IurretaLHII-proj/kolobot-mechanics/CAD/PINZA/pinza(bego)/6-dof-robotic-arm-kit-with-servo-motors-10231211.jpg

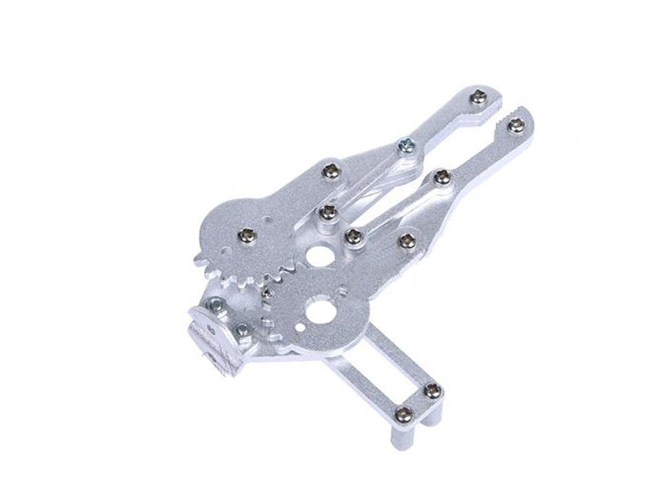
CAD/PINZA/pinza(bego)/6-dof-robotic-arm-kit-with-servo-motors-10231211.jpg
