IurretaLHII-proj/kolobot-mechanics/CAD/PINZA/pinza(bego)/AUREA.jpg

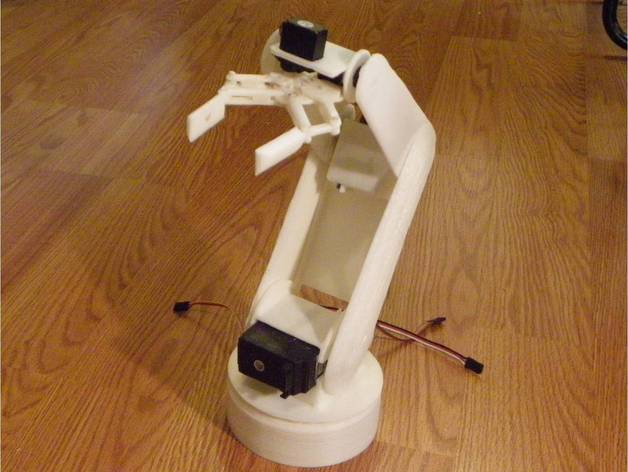
CAD/PINZA/pinza(bego)/AUREA.jpg
