IurretaLHII-proj/kolobot-mechanics/CAD/PINZA/pinza(bego)/descarga1.jpg

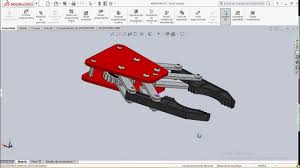
CAD/PINZA/pinza(bego)/descarga1.jpg
