IurretaLHII-proj/kolobot-mechanics/CAD/PINZA/pinza(bego)/descarga.jpg

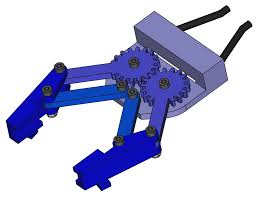
CAD/PINZA/pinza(bego)/descarga.jpg
