IurretaLHII-proj/kolobot-mechanics/CAD/PINZA/pinza(bego)/gripper2-solidworks.jpg

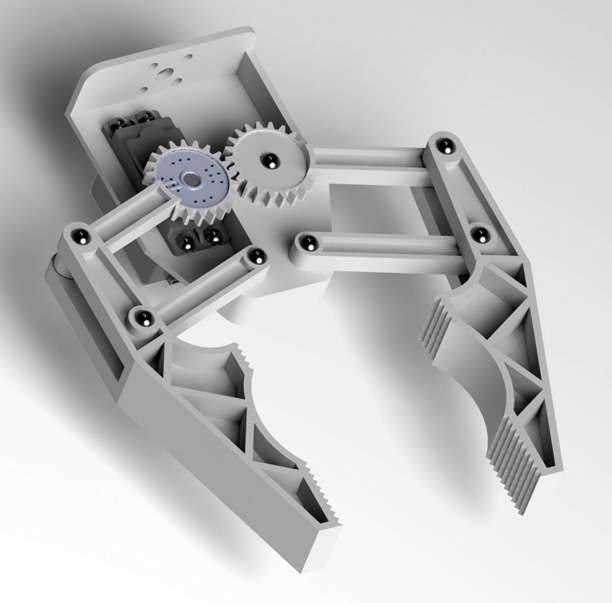
CAD/PINZA/pinza(bego)/gripper2-solidworks.jpg
