IurretaLHII-proj/kolobot-mechanics/CAD/PINZA/pinza(bego)/GRPA-KT-450x300.jpg

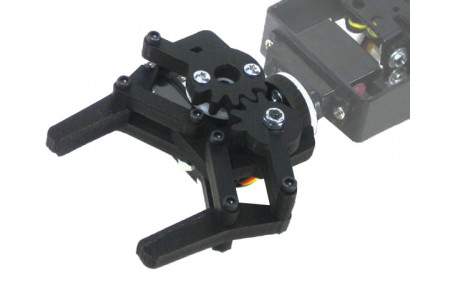
CAD/PINZA/pinza(bego)/GRPA-KT-450x300.jpg
