IurretaLHII-proj/kolobot-mechanics/CAD/PINZA/pinza(bego)/images1.jpg

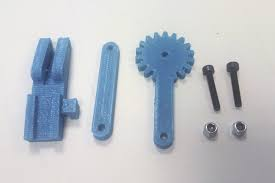
CAD/PINZA/pinza(bego)/images1.jpg
