IurretaLHII-proj/kolobot-mechanics/CAD/PINZA/pinza(bego)/images2.jpg

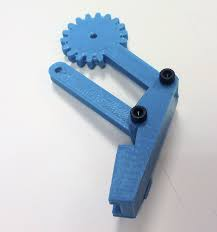
CAD/PINZA/pinza(bego)/images2.jpg
