IurretaLHII-proj/kolobot-mechanics/CAD/PINZA/pinza(bego)/images3.jpg

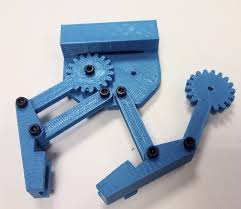
CAD/PINZA/pinza(bego)/images3.jpg
