IurretaLHII-proj/kolobot-mechanics/CAD/PINZA/pinza(bego)/AURREA/Arm_A3.stl

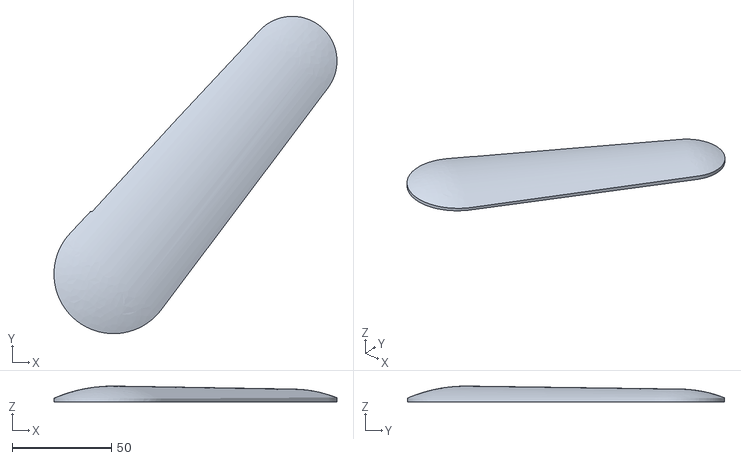
[picture p36: CAD file, 2022-01-14]
CAD/PINZA/pinza(bego)/AURREA/Arm_A3.stl
142.5 x 159.7 x 8.00
