IurretaLHII-proj/kolobot-mechanics/CAD/PINZA/pinza(bego)/robotic-arm-48.snapshot.6/MECCANO/PLASTIC GEAR.sldprt

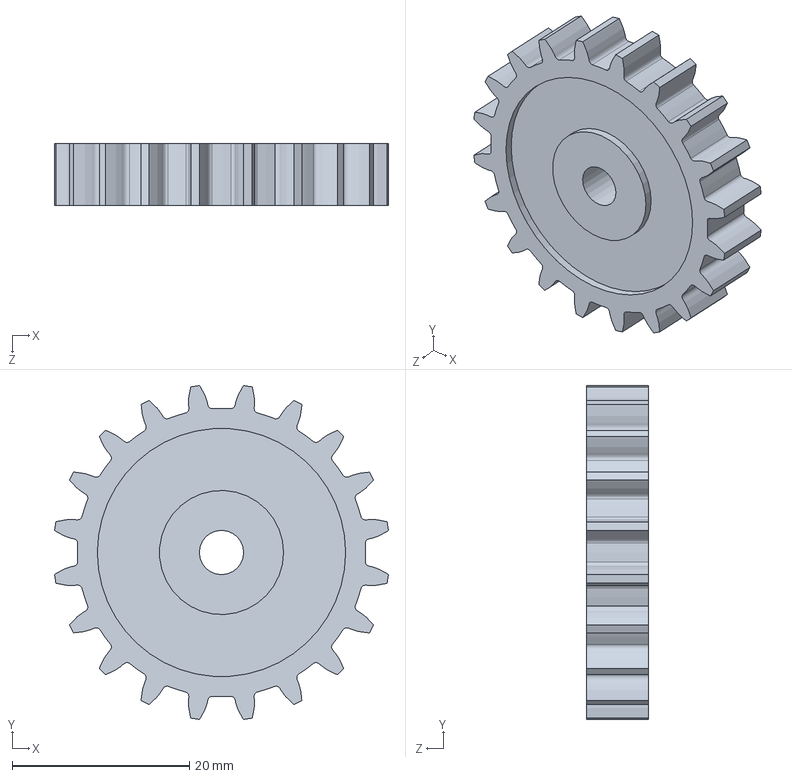
[picture p37: CAD file, 2022-01-14]
CAD/PINZA/pinza(bego)/robotic-arm-48.snapshot.6/MECCANO/PLASTIC GEAR.sldprt
37.7 x 37.7 x 7.00 mm
