IurretaLHII-proj/kolobot-mechanics/CAD/BIBRAZO/SOPORTE/tmp.stp

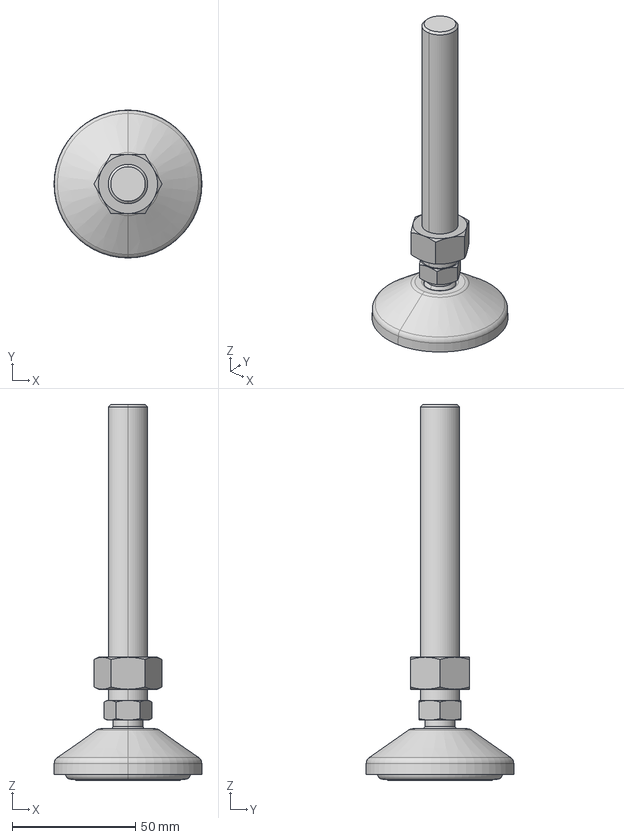
[picture p38: CAD file, 2022-01-14]
CAD/BIBRAZO/SOPORTE/tmp.stp
60.0 x 60.0 x 152.5 mm
