IurretaLHII-proj/kolobot-mechanics/CAD/PINZA/pinza(bego)/AURREA/Holder_omega_.stl

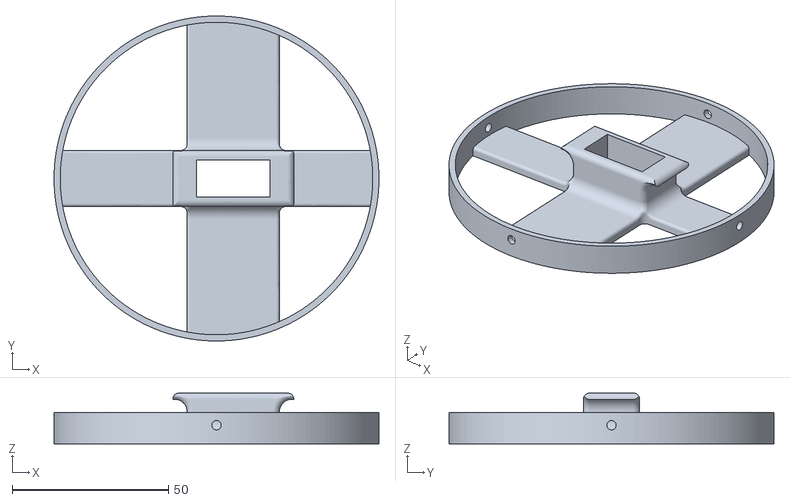
[picture p39: CAD file, 2022-01-14]
CAD/PINZA/pinza(bego)/AURREA/Holder_omega_.stl
104.0 x 104.0 x 16.3
