IurretaLHII-proj/kolobot-mechanics/CAD/PINZA/pinza(bego)/robotic-arm-48.snapshot.6/MECCANO/GRIP.sldprt

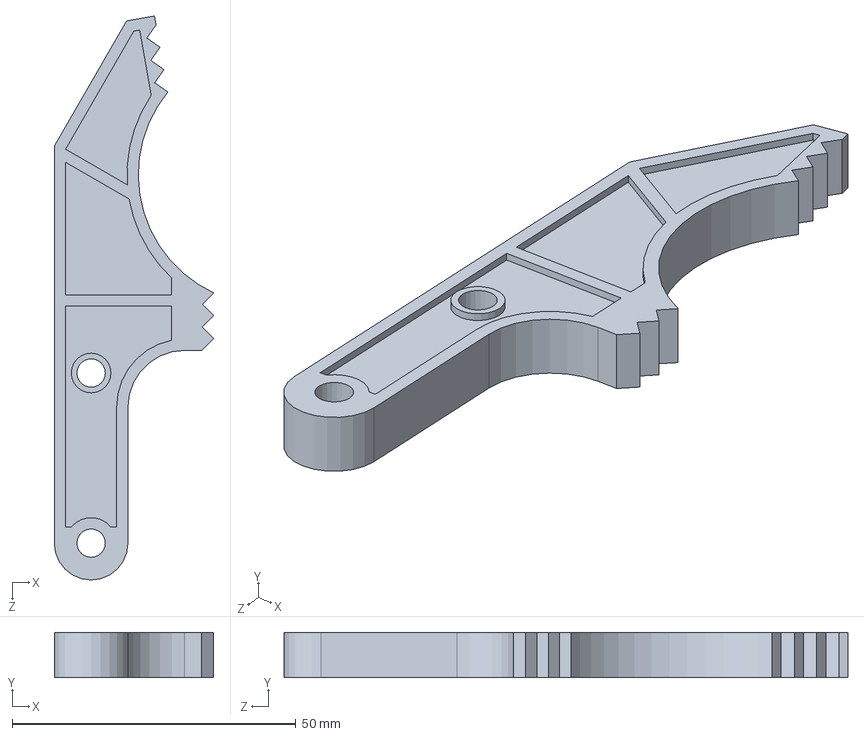
[picture p40: CAD file, 2022-01-14]
CAD/PINZA/pinza(bego)/robotic-arm-48.snapshot.6/MECCANO/GRIP.sldprt
28.1 x 8.00 x 99.5 mm
