IurretaLHII-proj/kolobot-mechanics/CAD/PINZA/STL artxiboak/CUBIERTA.stl

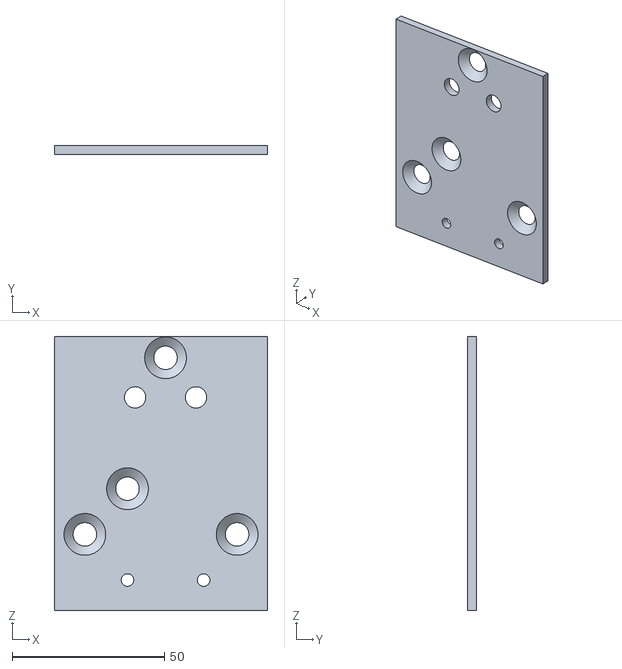
[picture p41: CAD file, 2022-01-14]
CAD/PINZA/STL artxiboak/CUBIERTA.stl
70.0 x 3.00 x 90.0
