IurretaLHII-proj/kolobot-mechanics/CAD/BIBRAZO/SOPORTE/21_0978_0_1.igs

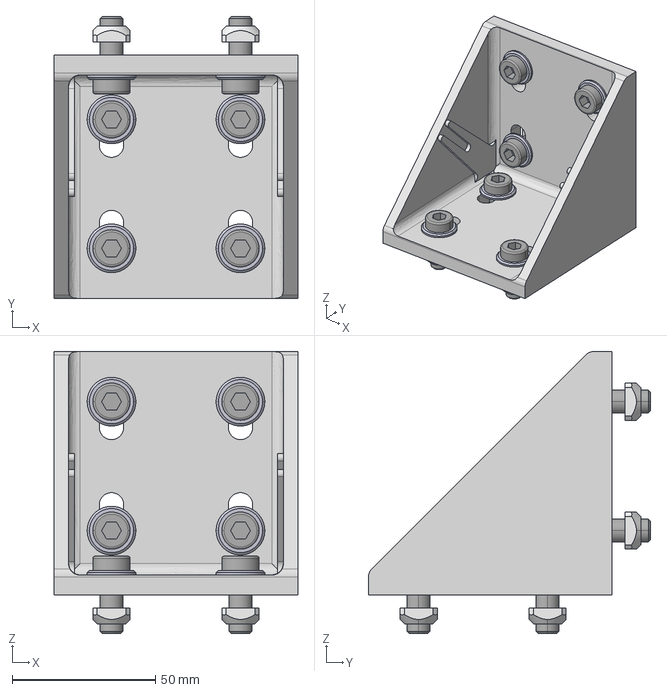
[picture p42: CAD file, 2022-01-14]
CAD/BIBRAZO/SOPORTE/21_0978_0_1.igs
85.0 x 98.4 x 98.4 mm
