IurretaLHII-proj/kolobot-mechanics/CAD/PINZA/pinza(bego)/AURREA/Arm_C3.stl

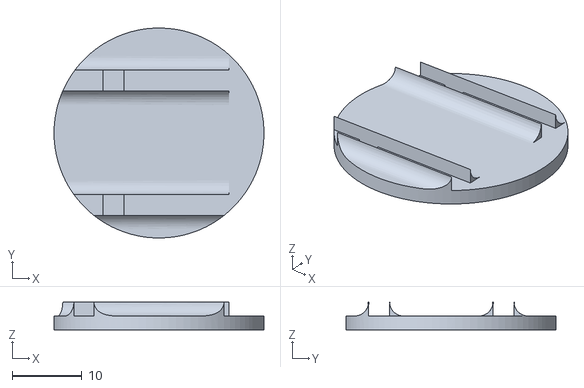
[picture p43: CAD file, 2022-01-14]
CAD/PINZA/pinza(bego)/AURREA/Arm_C3.stl
30.0 x 30.0 x 4.00
