IurretaLHII-proj/kolobot-mechanics/CAD/PINZA/pinza(bego)/robotic-arm-48.snapshot.6/MECCANO/BASE.SLDPRT

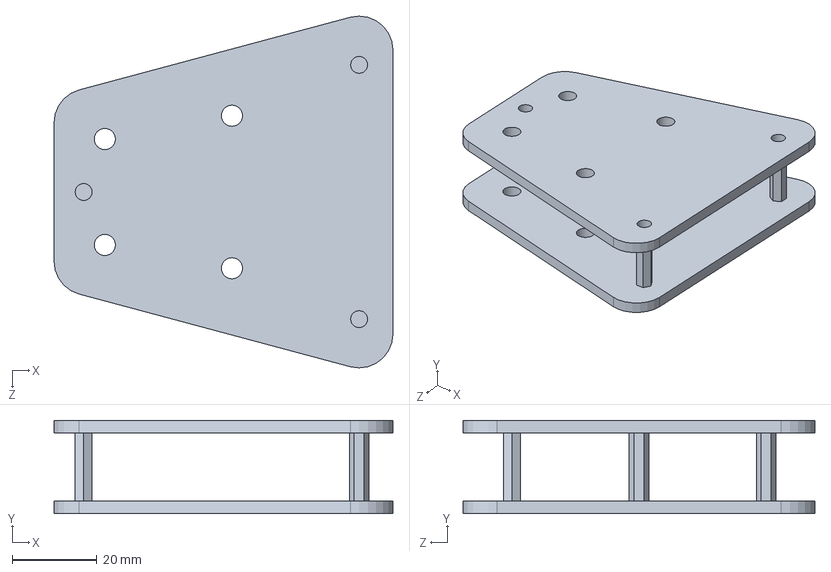
[picture p44: CAD file, 2022-01-14]
CAD/PINZA/pinza(bego)/robotic-arm-48.snapshot.6/MECCANO/BASE.SLDPRT
80.0 x 22.0 x 83.0 mm
