IurretaLHII-proj/kolobot-mechanics/CAD/PINZA/STL artxiboak/BRAZO PINZA (plastico-B).stl

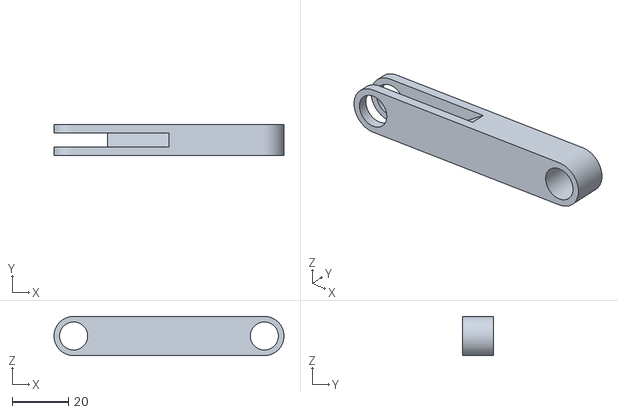
[picture p45: CAD file, 2022-01-14]
CAD/PINZA/STL artxiboak/BRAZO PINZA (plastico-B).stl
82.0 x 11.0 x 14.0
