IurretaLHII-proj/kolobot-mechanics/CAD/BIBRAZO/SOPORTE/21_1473_0_1.igs

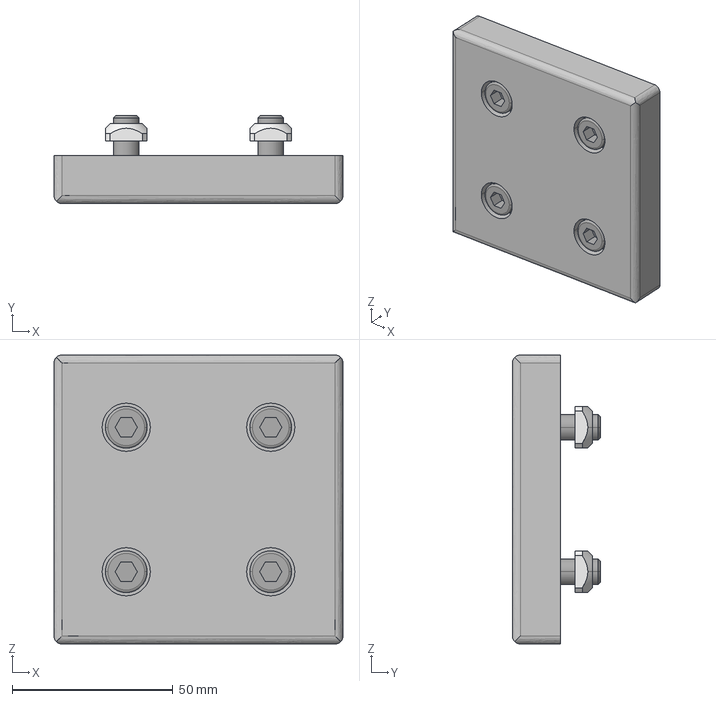
[picture p46: CAD file, 2022-01-14]
CAD/BIBRAZO/SOPORTE/21_1473_0_1.igs
90.0 x 27.5 x 90.0 mm
