IurretaLHII-proj/kolobot-mechanics/CAD/PINZA/pinza(bego)/AURREA/Arm_B3.stl

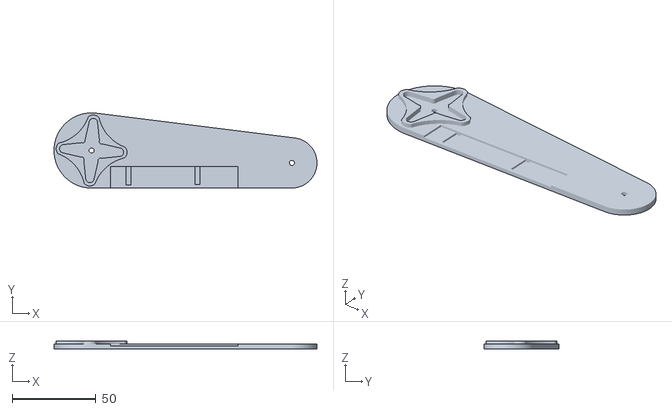
[picture p47: CAD file, 2022-01-14]
CAD/PINZA/pinza(bego)/AURREA/Arm_B3.stl
157.3 x 45.0 x 5.00
