IurretaLHII-proj/kolobot-mechanics/CAD/PINZA/pinza(bego)/robotic-arm-48.snapshot.6/MECCANO/ARM ROBOTIC.STEP

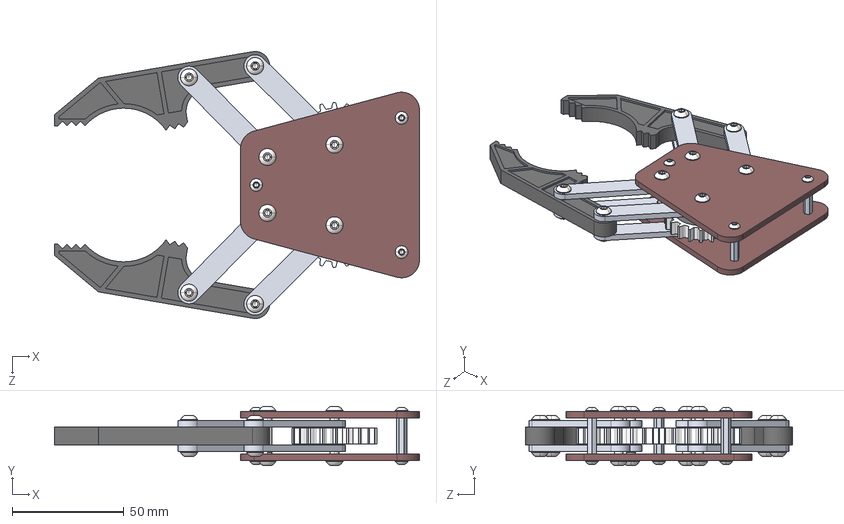
[picture p48: CAD file, 2022-01-14]
CAD/PINZA/pinza(bego)/robotic-arm-48.snapshot.6/MECCANO/ARM ROBOTIC.STEP
163.2 x 26.4 x 119.4 mm
socket button head cap screw_am_B18.3.4M - 4 x 0.7 x 4 SBHCS --N x 8
socket button head cap screw_am_B18.3.4M - 3 x 0.5 x 3 SBHCS --N x 6
BASE
socket button head cap screw_am_B18.3.4M - 4 x 0.7 x 8 SBHCS --N x 4
socket button head cap screw_am_B18.3.4M - 4 x 0.7 x 20 SBHCS --N x 4
PCS1 x 8
PLASTIC GEAR x 2
GRIP x 2
