IurretaLHII-proj/kolobot-mechanics/CAD/PINZA/STL artxiboak/ANTEBRAZO7.stl

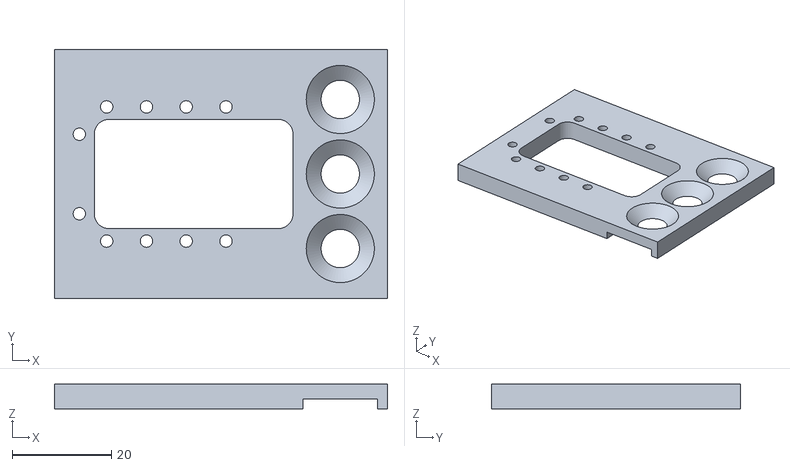
[picture p49: CAD file, 2022-01-14]
CAD/PINZA/STL artxiboak/ANTEBRAZO7.stl
67.0 x 50.0 x 5.00
