IurretaLHII-proj/kolobot-mechanics/CAD/PINZA/pinza(bego)/AURREA/Phalange_proximal_L.stl

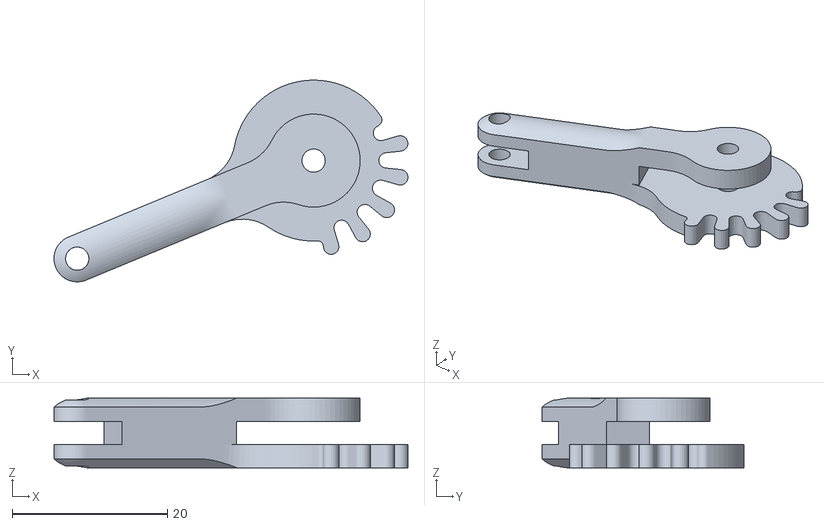
[picture p51: CAD file, 2022-01-14]
CAD/PINZA/pinza(bego)/AURREA/Phalange_proximal_L.stl
45.6 x 26.0 x 9.00
