IurretaLHII-proj/kolobot-mechanics/CAD/PINZA/STL artxiboak/BRAZO DE PLASTICO(sin cortar).stl

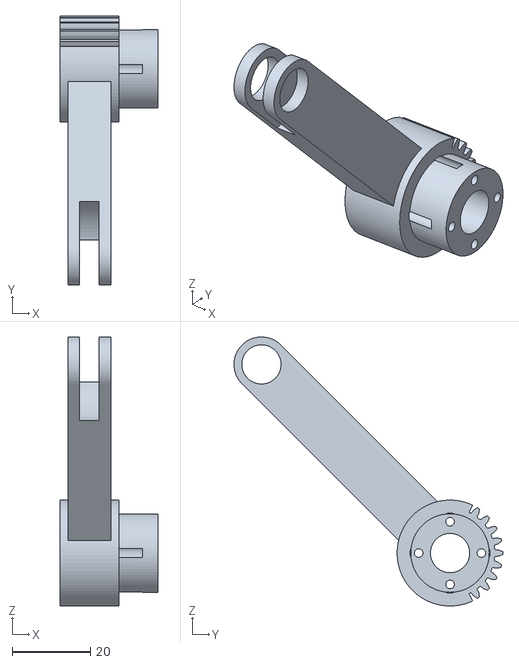
[picture p52: CAD file, 2022-01-14]
CAD/PINZA/STL artxiboak/BRAZO DE PLASTICO(sin cortar).stl
25.0 x 68.6 x 68.6
