IurretaLHII-proj/kolobot-mechanics/CAD/BIBRAZO/SOPORTE/20_1019_0_1_3.igs

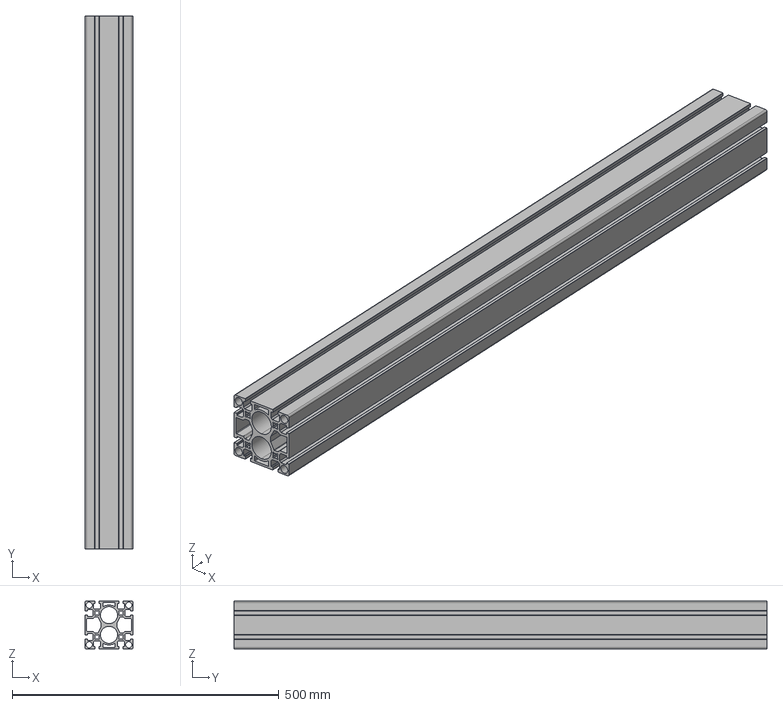
[picture p53: CAD file, 2022-01-14]
CAD/BIBRAZO/SOPORTE/20_1019_0_1_3.igs
90.0 x 1000.0 x 90.0 mm
