IurretaLHII-proj/kolobot-mechanics/CAD/PINZA/pinza(bego)/AURREA/Arm_A_.stl

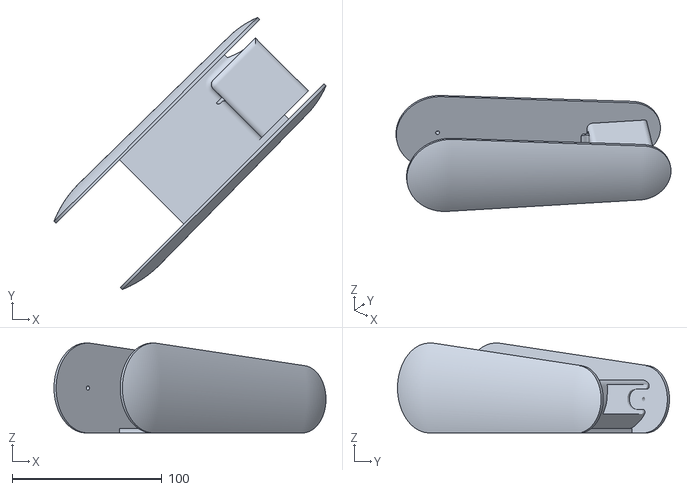
[picture p54: CAD file, 2022-01-14]
CAD/PINZA/pinza(bego)/AURREA/Arm_A_.stl
181.7 x 181.7 x 60.0
