IurretaLHII-proj/kolobot-mechanics/CAD/PINZA/STL artxiboak/BRAZO DE PLASTICO(cortado).stl

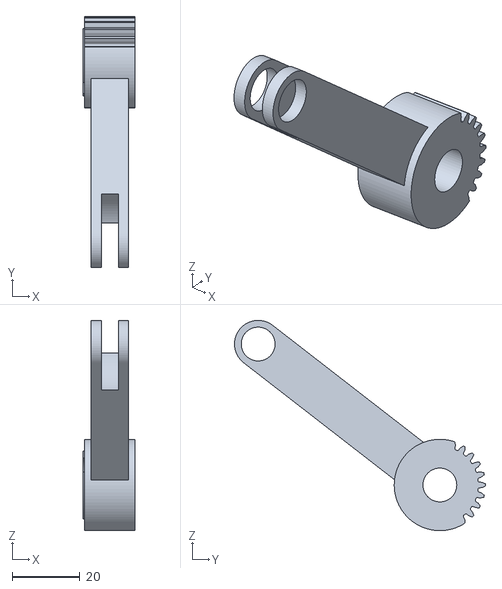
[picture p55: CAD file, 2022-01-14]
CAD/PINZA/STL artxiboak/BRAZO DE PLASTICO(cortado).stl
15.5 x 74.2 x 62.2
