IurretaLHII-proj/kolobot-mechanics/CAD/BIBRAZO/SOPORTE/22_1008_2_1.igs

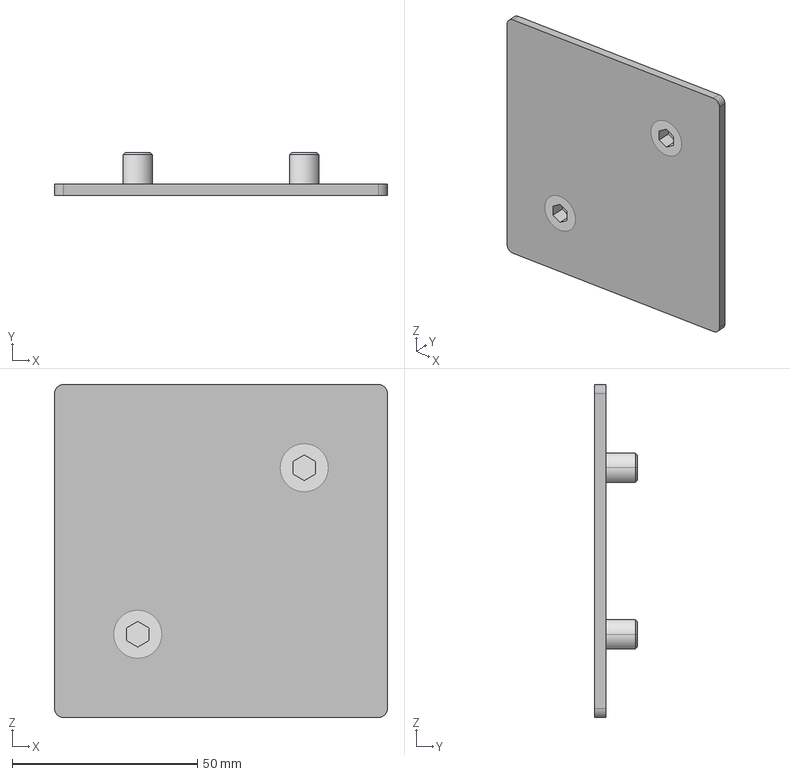
[picture p56: CAD file, 2022-01-14]
CAD/BIBRAZO/SOPORTE/22_1008_2_1.igs
90.0 x 11.5 x 90.0 mm
