IurretaLHII-proj/kolobot-mechanics/CAD/PINZA/pinza(bego)/AURREA/Arm_C2.stl

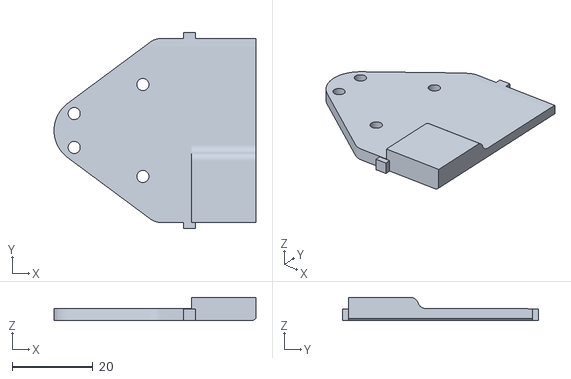
[picture p57: CAD file, 2022-01-14]
CAD/PINZA/pinza(bego)/AURREA/Arm_C2.stl
50.0 x 48.5 x 5.78
