IurretaLHII-proj/kolobot-mechanics/CAD/PINZA/STL artxiboak/GARRA plastico.stl

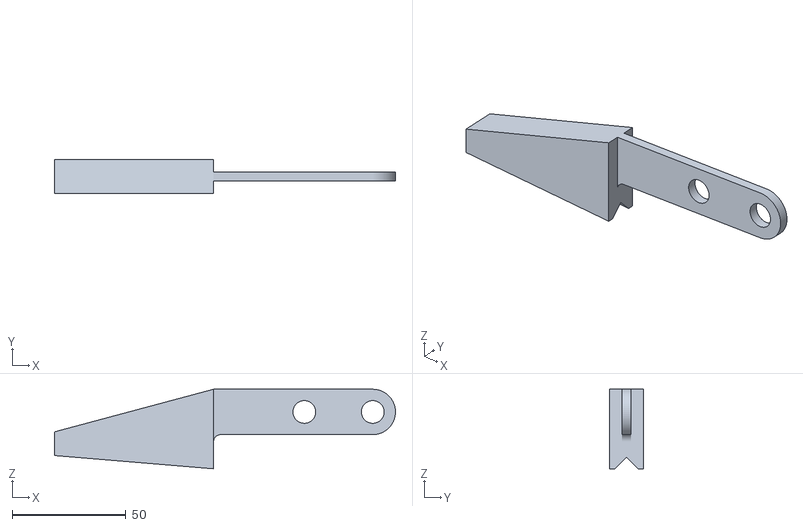
[picture p58: CAD file, 2022-01-14]
CAD/PINZA/STL artxiboak/GARRA plastico.stl
150.0 x 15.0 x 35.0
