IurretaLHII-proj/kolobot-mechanics/CAD/BIBRAZO/SOPORTE/20_1019_0_1_4.igs

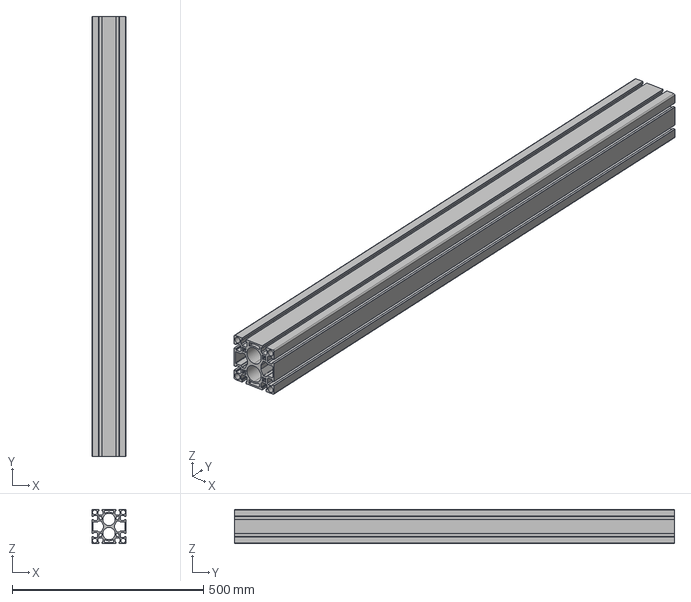
[picture p59: CAD file, 2022-01-14]
CAD/BIBRAZO/SOPORTE/20_1019_0_1_4.igs
90.0 x 1150.0 x 90.0 mm
