IurretaLHII-proj/kolobot-mechanics/CAD/PINZA/pinza(bego)/AURREA/Base_.stl

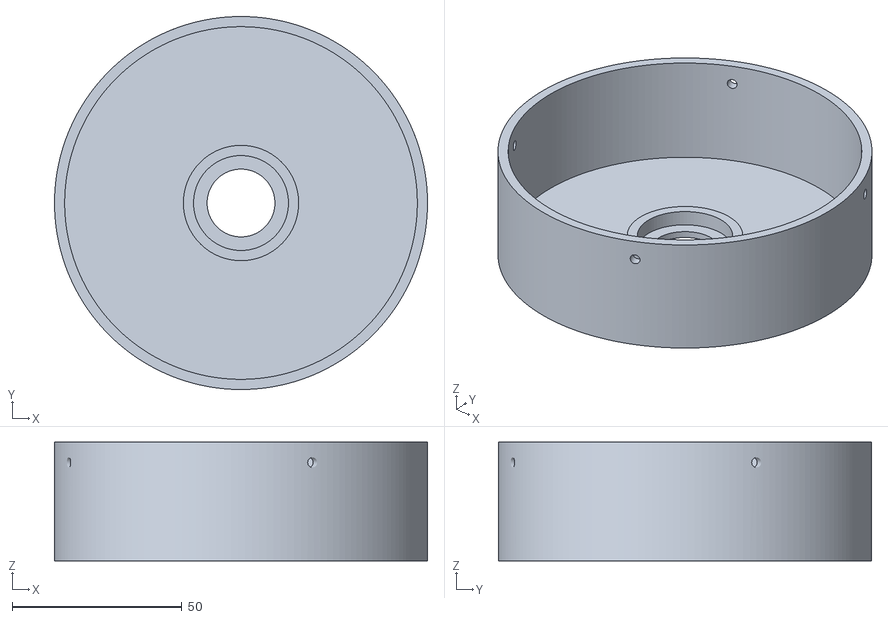
[picture p60: CAD file, 2022-01-14]
CAD/PINZA/pinza(bego)/AURREA/Base_.stl
110.0 x 110.0 x 35.0
