IurretaLHII-proj/kolobot-mechanics/CAD/PINZA/pinza(bego)/AURREA/Arm_B_.stl

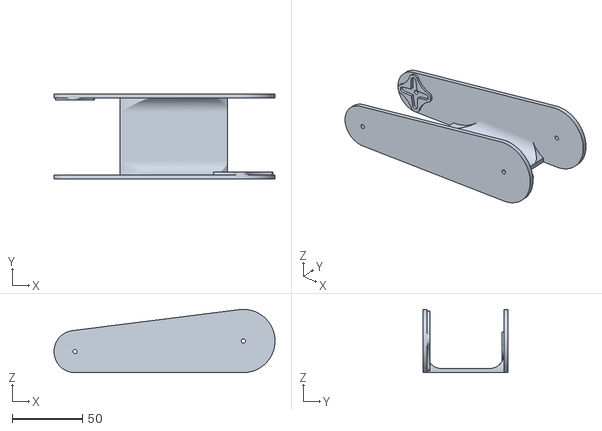
[picture p61: CAD file, 2022-01-14]
CAD/PINZA/pinza(bego)/AURREA/Arm_B_.stl
157.3 x 60.6 x 45.0
