IurretaLHII-proj/kolobot-mechanics/CAD/BIBRAZO/SOPORTE/20_1019_0_1_1.igs

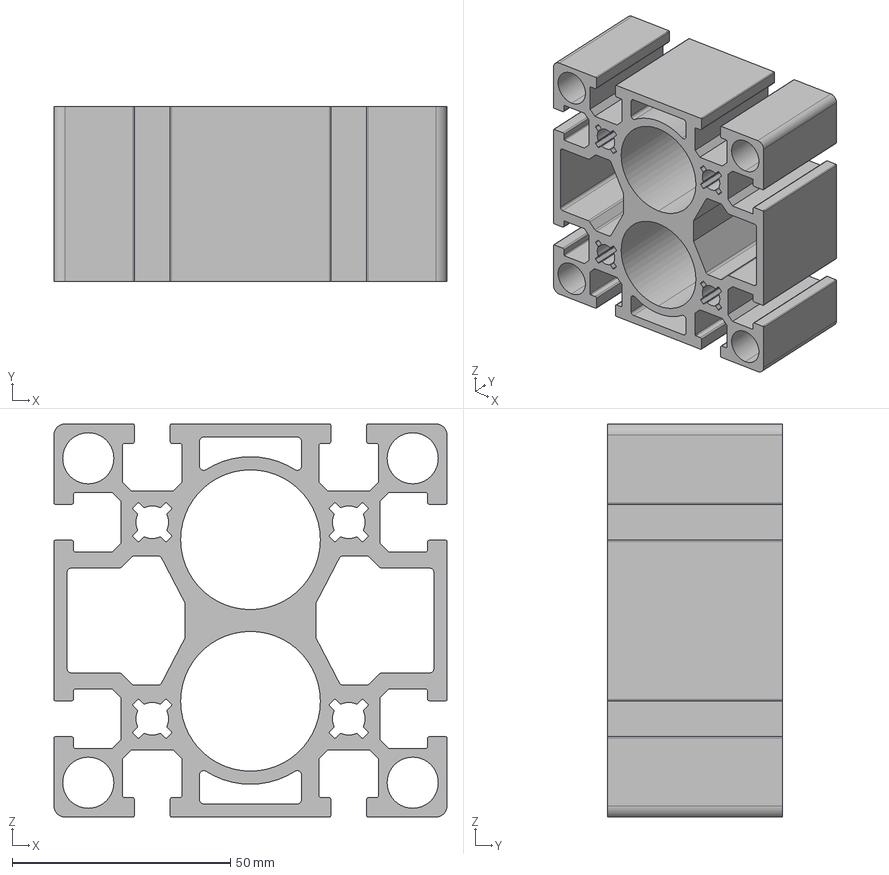
[picture p62: CAD file, 2022-01-14]
CAD/BIBRAZO/SOPORTE/20_1019_0_1_1.igs
90.0 x 40.0 x 90.0 mm
