IurretaLHII-proj/kolobot-mechanics/CAD/PINZA/pinza(bego)/AURREA/Arm_B2.stl

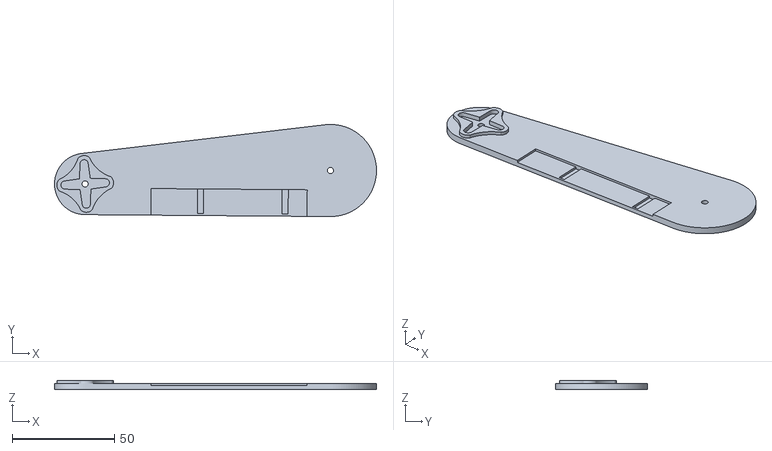
[picture p63: CAD file, 2022-01-14]
CAD/PINZA/pinza(bego)/AURREA/Arm_B2.stl
157.3 x 45.0 x 4.50
