IurretaLHII-proj/kolobot-mechanics/CAD/BIBRAZO/SOPORTE/20_1016_0_1.igs

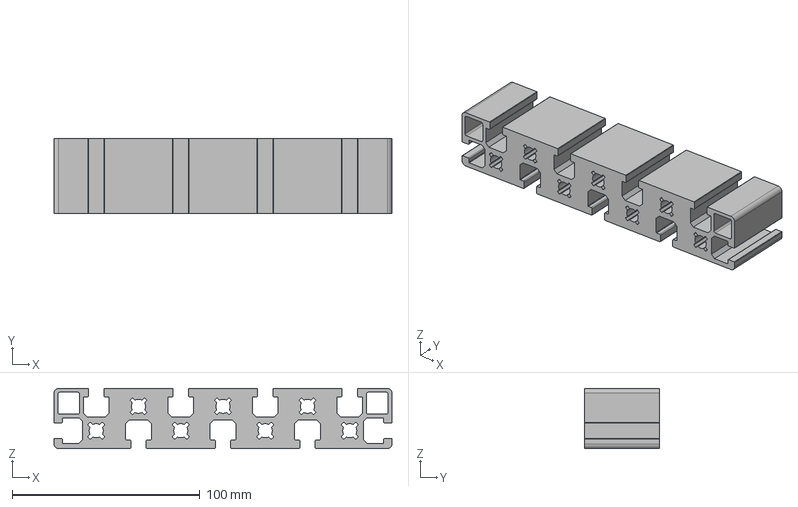
[picture p64: CAD file, 2022-01-14]
CAD/BIBRAZO/SOPORTE/20_1016_0_1.igs
180.0 x 40.0 x 32.0 mm
