IurretaLHII-proj/kolobot-mechanics/CAD/PINZA/pinza(bego)/AURREA/Phalange_medial.stl

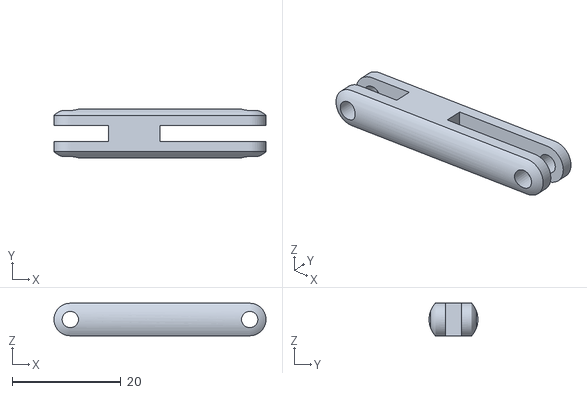
[picture p65: CAD file, 2022-01-14]
CAD/PINZA/pinza(bego)/AURREA/Phalange_medial.stl
39.0 x 9.00 x 6.00
