IurretaLHII-proj/kolobot-mechanics/CAD/PINZA/pinza(bego)/AURREA/Arm_C1.stl

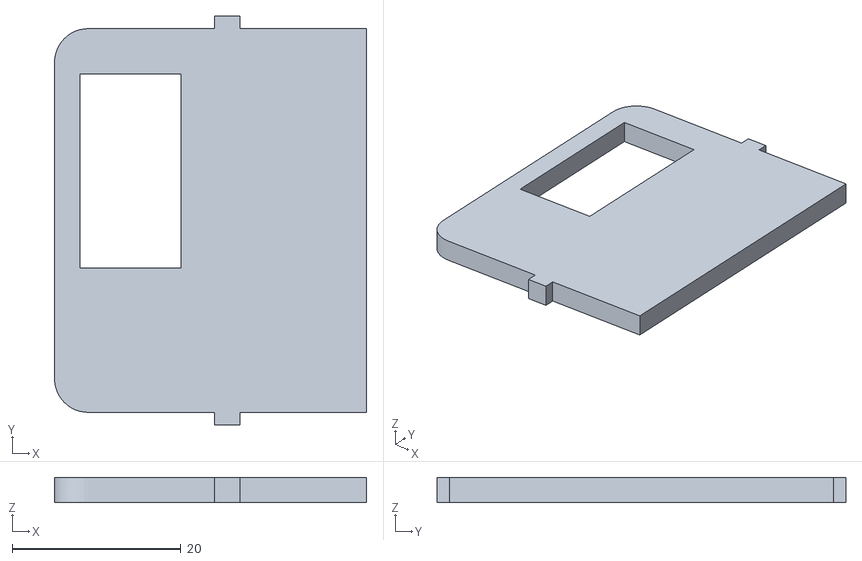
[picture p66: CAD file, 2022-01-14]
CAD/PINZA/pinza(bego)/AURREA/Arm_C1.stl
37.0 x 48.5 x 3.00
