IurretaLHII-proj/kolobot-mechanics/CAD/PINZA/pinza(bego)/AURREA/Arm_B1.stl

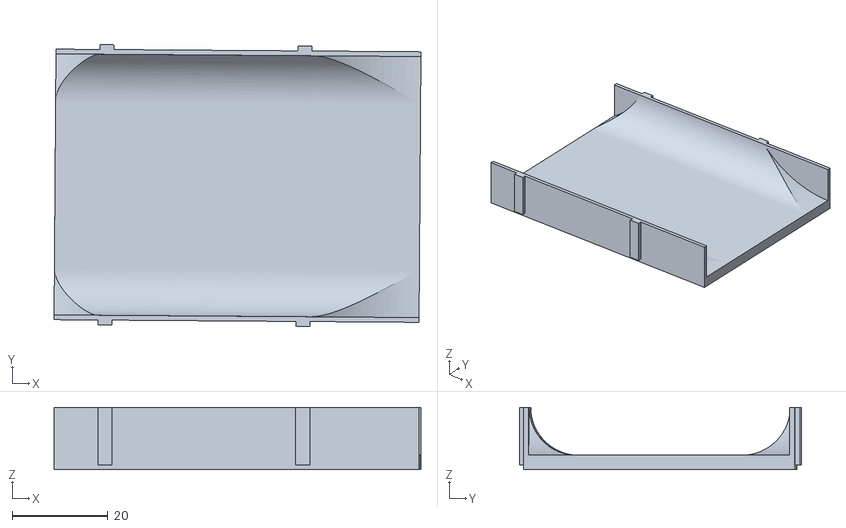
[picture p67: CAD file, 2022-01-14]
CAD/PINZA/pinza(bego)/AURREA/Arm_B1.stl
76.8 x 58.9 x 13.0
