IurretaLHII-proj/kolobot-mechanics/CAD/PINZA/pinza(bego)/AURREA/Arm_C.stl

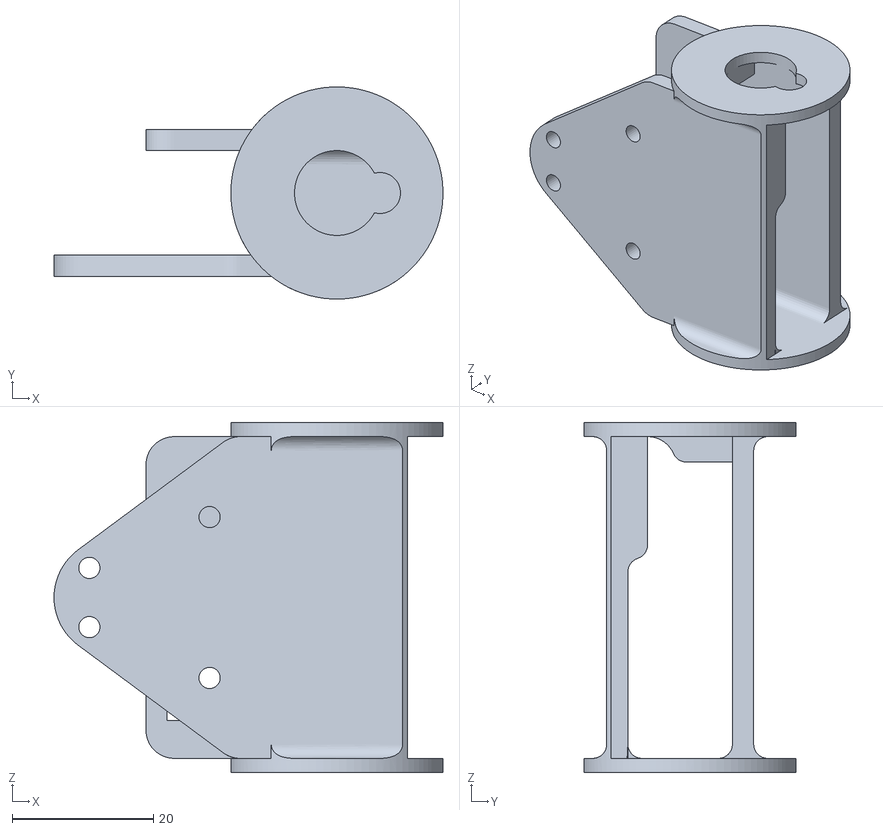
[picture p68: CAD file, 2022-01-14]
CAD/PINZA/pinza(bego)/AURREA/Arm_C.stl
55.0 x 30.0 x 49.5
