IurretaLHII-proj/kolobot-mechanics/CAD/PINZA/pinza(bego)/AURREA/Arm_C4.stl

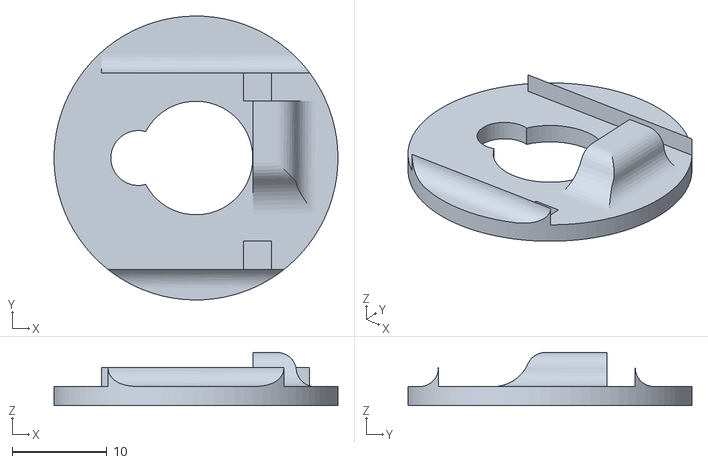
[picture p69: CAD file, 2022-01-14]
CAD/PINZA/pinza(bego)/AURREA/Arm_C4.stl
30.0 x 30.0 x 5.60
