IurretaLHII-proj/kolobot-mechanics/CAD/PINZA/pinza(bego)/AURREA/Phalange_distal_L.stl

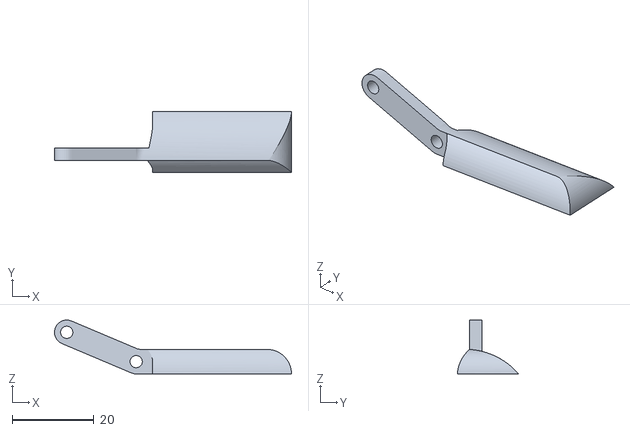
[picture p70: CAD file, 2022-01-14]
CAD/PINZA/pinza(bego)/AURREA/Phalange_distal_L.stl
58.0 x 15.0 x 13.2
