IurretaLHII-proj/kolobot-mechanics/CAD/PINZA/pinza(bego)/AURREA/Arm_A1_.stl

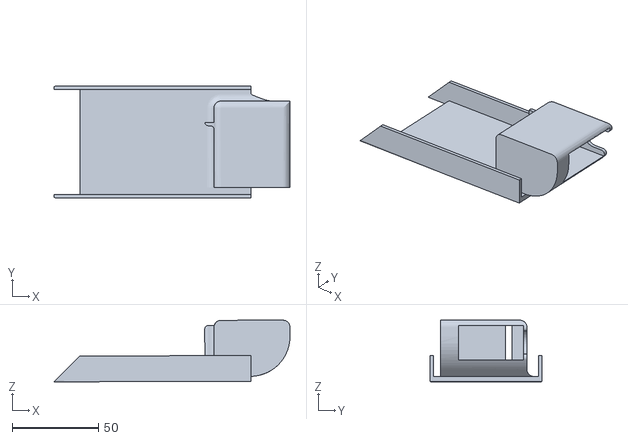
[picture p71: CAD file, 2022-01-14]
CAD/PINZA/pinza(bego)/AURREA/Arm_A1_.stl
136.6 x 64.6 x 35.7
