IurretaLHII-proj/kolobot-mechanics/CAD/PINZA/pinza(bego)/AURREA/Cross_omega_.stl

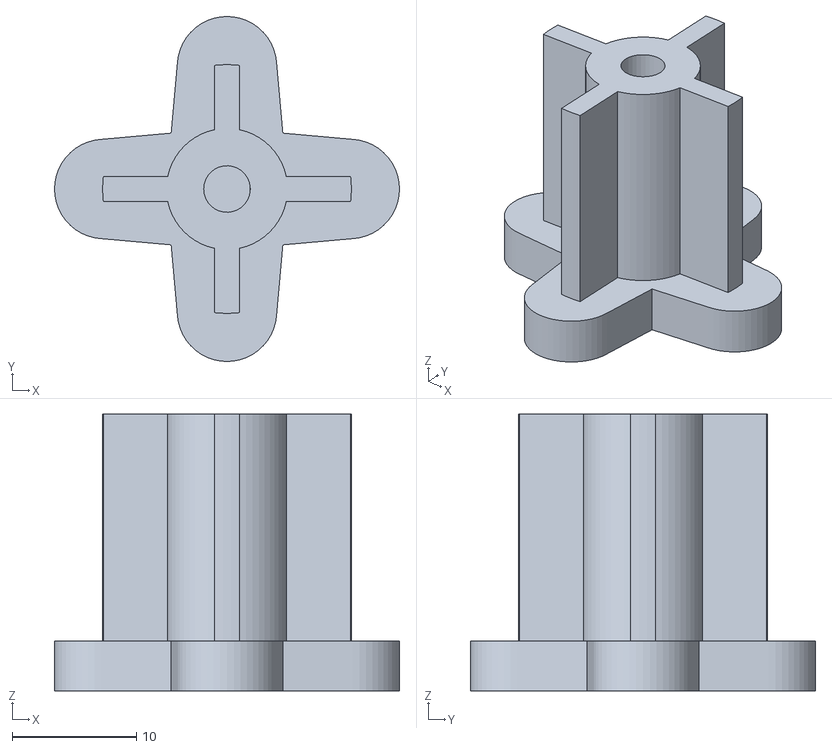
[picture p72: CAD file, 2022-01-14]
CAD/PINZA/pinza(bego)/AURREA/Cross_omega_.stl
27.8 x 27.8 x 22.2
