IurretaLHII-proj/kolobot-mechanics/CAD/PINZA/pinza(bego)/AURREA/AURA.stl

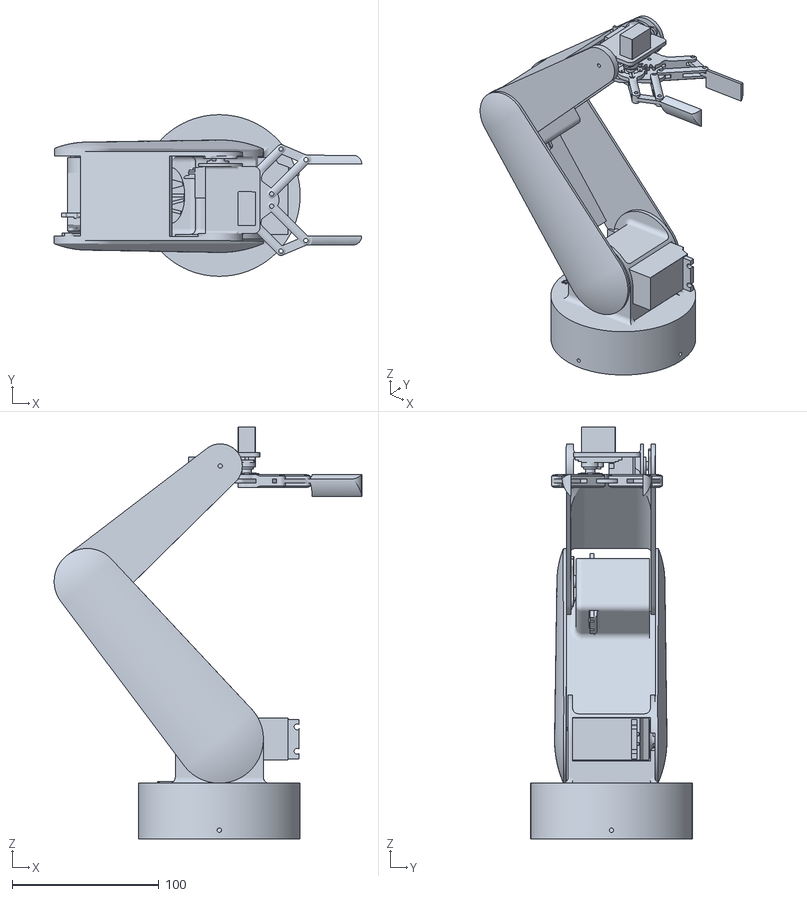
[picture p73: CAD file, 2022-01-14]
CAD/PINZA/pinza(bego)/AURREA/AURA.stl
209.5 x 110.0 x 280.5
