IurretaLHII-proj/kolobot-mechanics/CAD/PINZA/pinza(bego)/AURREA/Arm_A2.stl

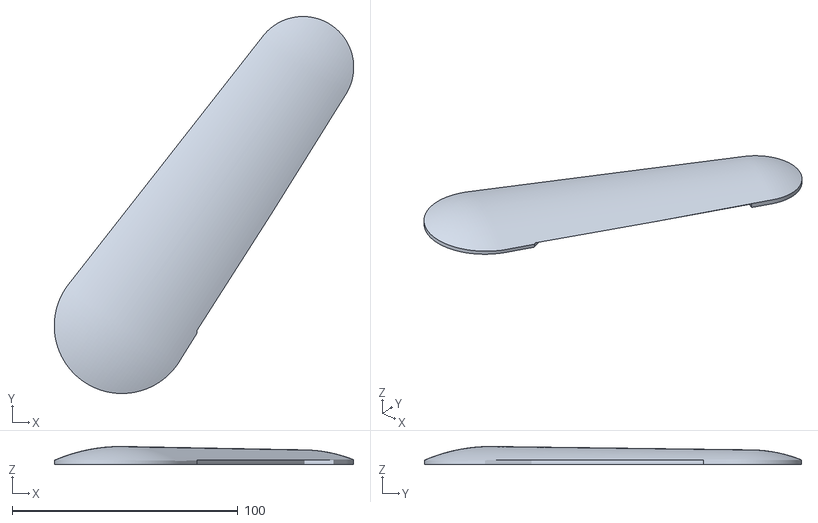
[picture p74: CAD file, 2022-01-14]
CAD/PINZA/pinza(bego)/AURREA/Arm_A2.stl
132.8 x 167.2 x 8.00
