IurretaLHII-proj/kolobot-mechanics/CAD/PINZA/pinza(bego)/AURREA/Phalnge_proximal_R.stl

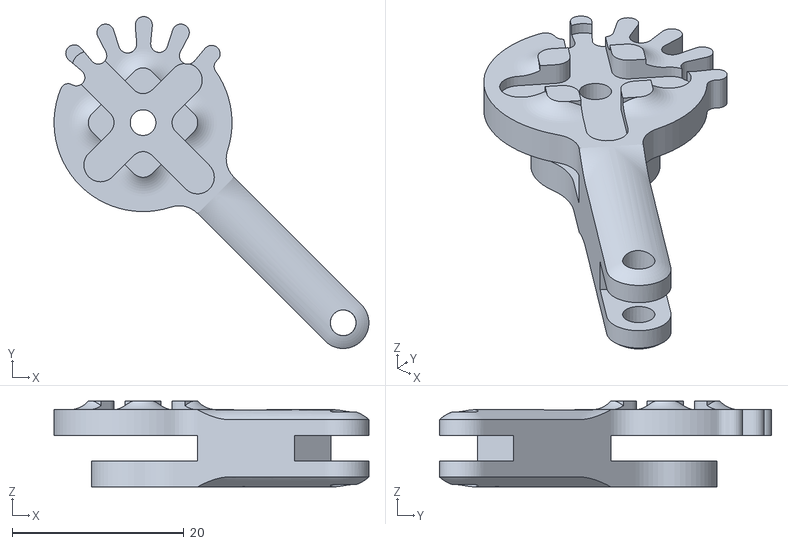
[picture p75: CAD file, 2022-01-14]
CAD/PINZA/pinza(bego)/AURREA/Phalnge_proximal_R.stl
36.7 x 38.7 x 10.0
